E-Hajj/Ahmad/image/case5.PNG

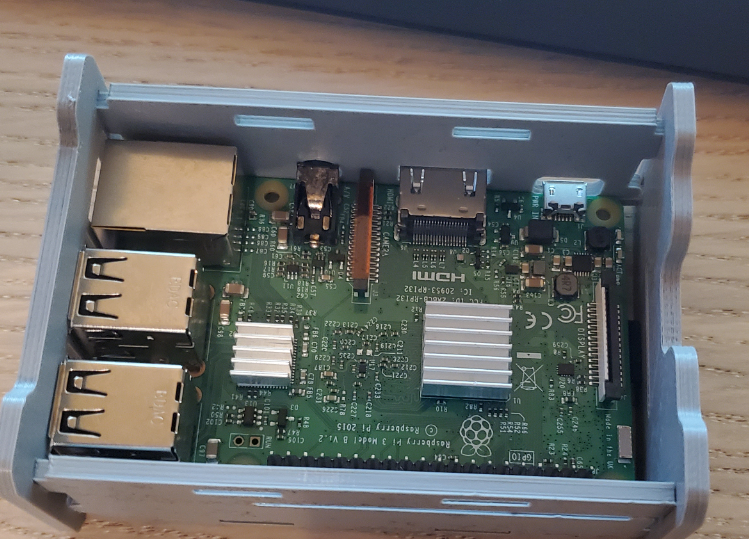
image/case5.PNG
