E-Hajj/Ahmad/image/sensorScrew.PNG

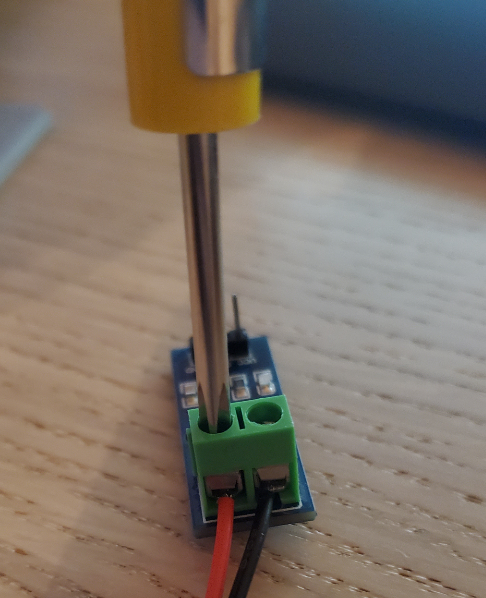
image/sensorScrew.PNG
