E-Hajj/Ahmad/image/sidepanel.PNG

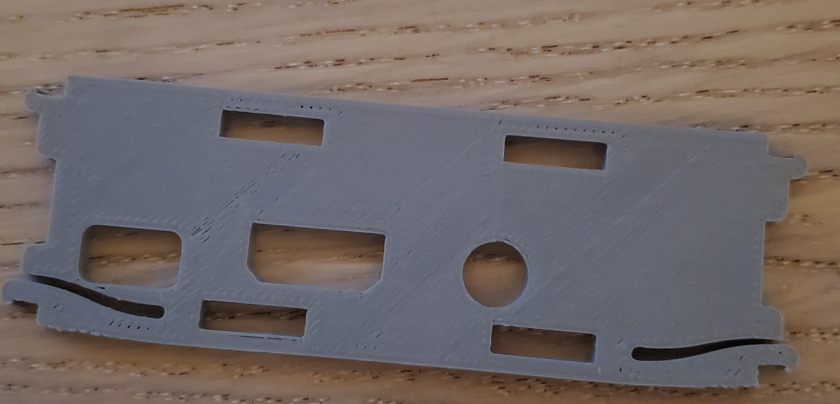
image/sidepanel.PNG
